Raresreras/Plantlink/receiver/receiver.kicad_sch

## KiCad design receiver/receiver.kicad_sch (2024-07-23)

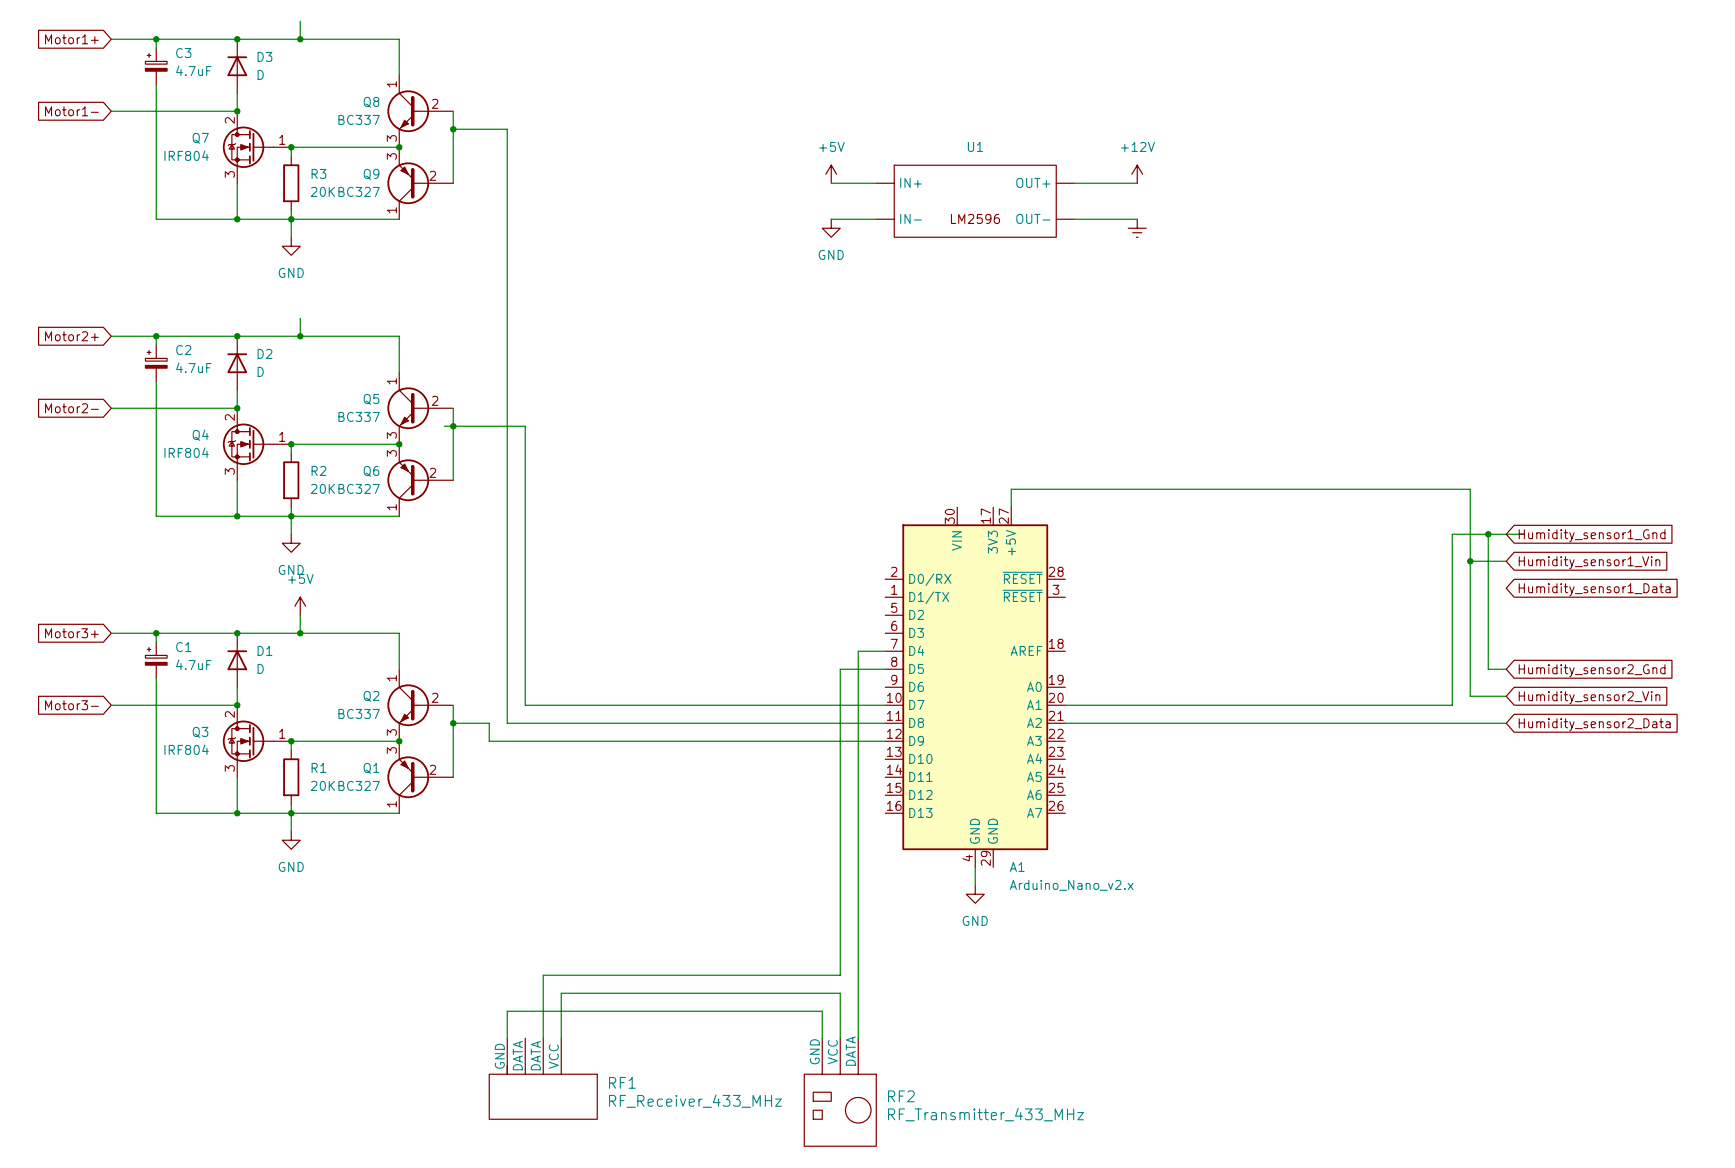
[picture p9: schematic receiver.kicad_sch]

Parts:
A1: Arduino_Nano_v2.x; Arduino_Nano
C1, C2, C3: 4.7uF
D1, D2, D3: D
Q1, Q6, Q9: BC327; TO-92_Inline
Q2, Q5, Q8: BC337; TO-92_Inline
Q3, Q4, Q7: IRF804; TO-220-3_Vertical
R1, R2, R3: 20K
RF1: RF_Receiver_433_MHz
RF2: RF_Transmitter_433_MHz
U1: (no value)

Connections:
+5V: C1.1, D1.1 (K), Q2.1 (C), U1.
+12V: U1.
Earth: U1.
GND: A1.4 (GND), C1.2, C2.2, C3.2, Q1.1 (C), Q3.3 (S), Q4.3 (S), Q6.1 (C), Q7.3 (S), Q9.1 (C), R1.2, R2.2, R3.2, U1.
Humidity_sensor1_Gnd: A1.20 (A1)
Humidity_sensor1_Vin: A1.27 (+5V)
Humidity_sensor2_Data: A1.21 (A2)
Motor1+: C3.1, D3.1 (K), Q8.1 (C)
Motor1-: D3.2 (A), Q7.2 (D)
Motor2+: C2.1, D2.1 (K), Q5.1 (C)
Motor2-: D2.2 (A), Q4.2 (D)
Motor3-: D1.2 (A), Q3.2 (D)
unnamed: A1.7 (D4), RF2.1 (DATA)
unnamed: A1.8 (D5), RF1.2 (DATA)
unnamed: A1.10 (D7), Q5.2 (B), Q6.2 (B)
unnamed: A1.11 (D8), Q8.2 (B), Q9.2 (B)
unnamed: A1.12 (D9), Q1.2 (B), Q2.2 (B)
unnamed: Q1.3 (E), Q2.3 (E), Q3.1 (G), R1.1
unnamed: Q4.1 (G), Q5.3 (E), Q6.3 (E), R2.1
unnamed: Q7.1 (G), Q8.3 (E), Q9.3 (E), R3.1
unnamed: RF1.1 (VCC), RF2.2 (VCC)
unnamed: RF1.4 (GND), RF2.3 (GND)
