Raresreras/Plantlink/sensor v1/sensor v1.kicad_sch

## KiCad design sensor v1/sensor v1.kicad_sch (2024-07-30)

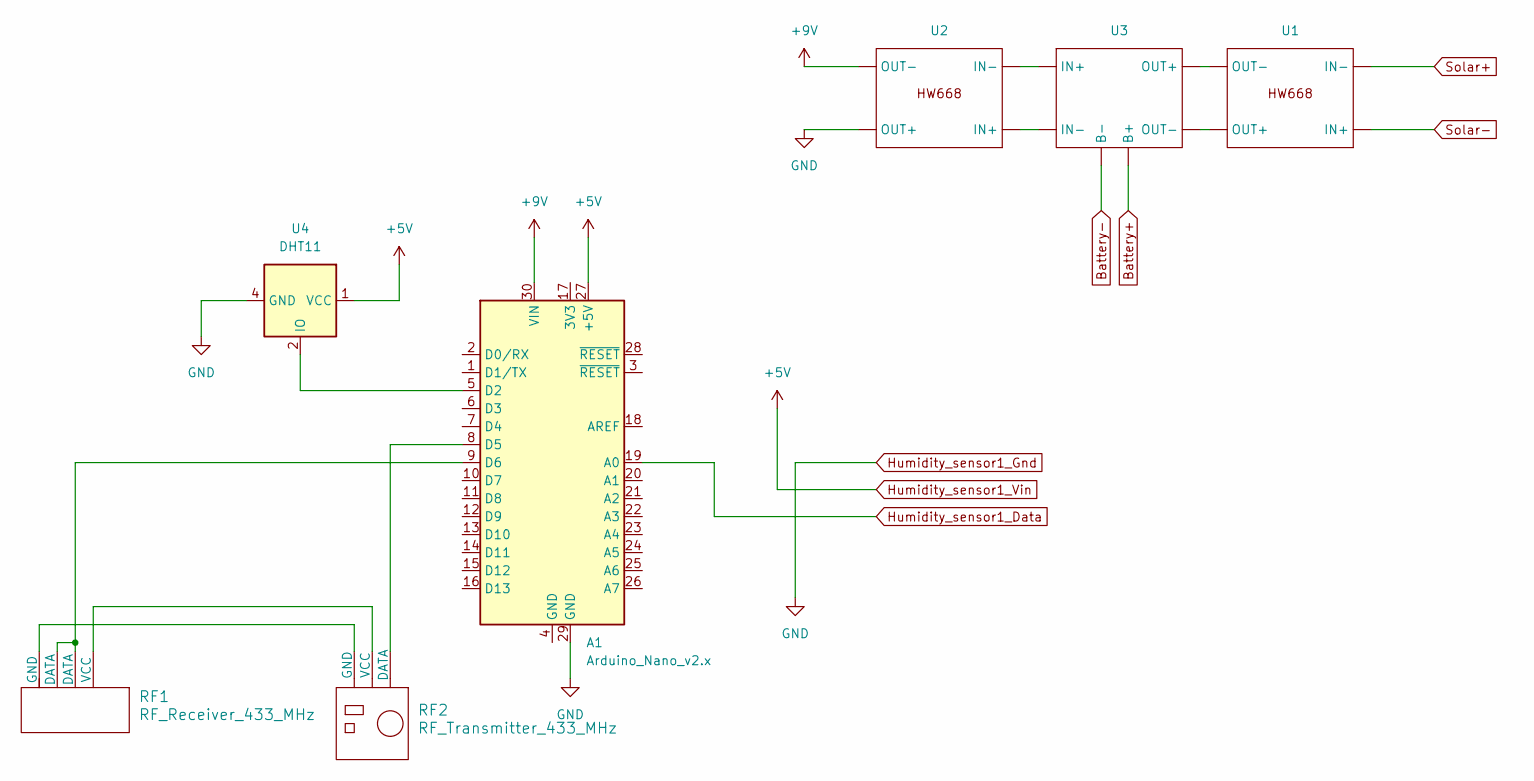
[picture p10: schematic sensor v1.kicad_sch]

Parts:
A1: Arduino_Nano_v2.x; Arduino_Nano
RF1: RF_Receiver_433_MHz
RF2: RF_Transmitter_433_MHz
U1, U2, U3: (no value)
U4: DHT11; Aosong_DHT11_5.5x12.0_P2.54mm

Connections:
+5V: A1.27 (+5V), U4.1 (VCC)
+9V: A1.30 (VIN), U2.
Battery+: U3.
Battery-: U3.
GND: A1.29 (GND), U2., U4.4 (GND)
Humidity_sensor1_Data: A1.19 (A0)
unnamed: A1.5 (D2), U4.2 (IO)
unnamed: A1.8 (D5), RF2.1 (DATA)
unnamed: A1.9 (D6), RF1.2 (DATA), RF1.3 (DATA)
unnamed: RF1.1 (VCC), RF2.2 (VCC)
unnamed: RF1.4 (GND), RF2.3 (GND)
unnamed: U1., U3.
unnamed: U2., U3.
Solar+: U1.
Solar-: U1.
